arglurgl/rocketlogger/platformio/src/format_flash/format_flash.cpp

// modified Adafruit example to be called from main.cpp

// Adafruit SPI Flash FatFs Format Example
// Author: Tony DiCola
//
// !!!!!!!!!!!!!!!!!!!!!!!!!!!!!!!!!!!!!!!!!!!!!!!!!!!!!!!!!!!!!
// !!  NOTE: YOU WILL ERASE ALL DATA BY RUNNING THIS SKETCH!  !!
// !!!!!!!!!!!!!!!!!!!!!!!!!!!!!!!!!!!!!!!!!!!!!!!!!!!!!!!!!!!!!
//
// Usage:
// - Modify the pins and type of fatfs object in the config
//   section below if necessary (usually not necessary).
// - Upload this sketch to your M0 express board.
// - Open the serial monitor at 115200 baud.  You should see a
//   prompt to confirm formatting.  If you don't see the prompt
//   close the serial monitor, press the board reset buttton,
//   wait a few seconds, then open the serial monitor again.
// - Type OK and enter to confirm the format when prompted.
// - Partitioning and formatting will take about 30-60 seconds.
//   Once formatted a message will be printed to notify you that
//   it is finished.
//
#include <SPI.h>
#include <SdFat.h>
#include <Adafruit_SPIFlash.h>

// Since SdFat doesn't fully support FAT12 such as format a new flash
// We will use Elm Cham's fatfs f_mkfs() to format
#include "ff.h"
#include "diskio.h"

// up to 11 characters
#define DISK_LABEL    "EXT FLASH"

// for flashTransport definition
//#include "flash_config.h" already done in main

extern Adafruit_SPIFlash flash; //declared in main

void format_fat12(void)
{
  // Working buffer for f_mkfs.
  #ifdef __AVR__
    uint8_t workbuf[512];
  #else
    uint8_t workbuf[4096];
  #endif

  // Elm Cham's fatfs objects
  FATFS elmchamFatfs;

  // Make filesystem.
  FRESULT r = f_mkfs("", FM_FAT, 0, workbuf, sizeof(workbuf));
  if (r != FR_OK) {
    Serial.print(F("Error, f_mkfs failed with error code: ")); Serial.println(r, DEC);
    while(1) yield();
  }

  // mount to set disk label
  r = f_mount(&elmchamFatfs, "0:", 1);
  if (r != FR_OK) {
    Serial.print(F("Error, f_mount failed with error code: ")); Serial.println(r, DEC);
    while(1) yield();
  }

  // Setting label
  Serial.println(F("Setting disk label to: " DISK_LABEL));
  r = f_setlabel(DISK_LABEL);
  if (r != FR_OK) {
    Serial.print(F("Error, f_setlabel failed with error code: ")); Serial.println(r, DEC);
    while(1) yield();
  }

  // unmount
  f_unmount("0:");

  // sync to make sure all data is written to flash
  flash.syncBlocks();

  Serial.println(F("Formatted flash!"));
}

void check_fat12(void)
{
  // Check new filesystem
  FatVolume fatfs;
  if (!fatfs.begin(&flash)) {
    Serial.println(F("Error, failed to mount newly formatted filesystem!"));
    while(1) delay(1);
  }
}


void format_flash() {
  // serial port: wait for it to open before continuing.
  while (!Serial) delay(100);
  
  Serial.println(F("Adafruit SPI Flash FatFs Format Example"));

  // Initialize flash library and check its chip ID.
  if (!flash.begin()) {
    Serial.println(F("Error, failed to initialize flash chip!"));
    while(1) yield();
  }

  Serial.print(F("Flash chip JEDEC ID: 0x")); Serial.println(flash.getJEDECID(), HEX);
  Serial.print(F("Flash size: ")); Serial.print(flash.size() / 1024); Serial.println(F(" KB"));

  // Uncomment to flash LED while writing to flash
  // flash.setIndicator(LED_BUILTIN, true);

  // Wait for user to send OK to continue.
  Serial.setTimeout(30000);  // Increase timeout to print message less frequently.
  do {
    Serial.println(F("!!!!!!!!!!!!!!!!!!!!!!!!!!!!!!!!!!!!!!!!!!!!!!!!!!!!!!!!!!!!!!!!!!!!!"));
    Serial.println(F("This will ERASE ALL DATA on the flash chip and format it with a new filesystem!"));
    Serial.println(F("Type OK (all caps) and press enter to continue."));
    Serial.println(F("!!!!!!!!!!!!!!!!!!!!!!!!!!!!!!!!!!!!!!!!!!!!!!!!!!!!!!!!!!!!!!!!!!!!!"));
  } while ( !Serial.find((char*) "OK"));

  // Call fatfs begin and passed flash object to initialize file system
  Serial.println(F("Creating and formatting FAT filesystem (this takes ~60 seconds)..."));

  format_fat12();

  check_fat12();

  // Done!
  Serial.println(F("Flash chip successfully formatted with new empty filesystem! Please restart board."));

  while(1)
    {
      yield();
      delay(1);
    }
}

//--------------------------------------------------------------------+
// fatfs diskio
//--------------------------------------------------------------------+
extern "C"
{

DSTATUS disk_status ( BYTE pdrv )
{
  (void) pdrv;
	return 0;
}

DSTATUS disk_initialize ( BYTE pdrv )
{
  (void) pdrv;
	return 0;
}

DRESULT disk_read (
	BYTE pdrv,		/* Physical drive nmuber to identify the drive */
	BYTE *buff,		/* Data buffer to store read data */
	DWORD sector,	/* Start sector in LBA */
	UINT count		/* Number of sectors to read */
)
{
  (void) pdrv;
	return flash.readBlocks(sector, buff, count) ? RES_OK : RES_ERROR;
}

DRESULT disk_write (
	BYTE pdrv,			/* Physical drive nmuber to identify the drive */
	const BYTE *buff,	/* Data to be written */
	DWORD sector,		/* Start sector in LBA */
	UINT count			/* Number of sectors to write */
)
{
  (void) pdrv;
  return flash.writeBlocks(sector, buff, count) ? RES_OK : RES_ERROR;
}

DRESULT disk_ioctl (
	BYTE pdrv,		/* Physical drive nmuber (0..) */
	BYTE cmd,		/* Control code */
	void *buff		/* Buffer to send/receive control data */
)
{
  (void) pdrv;

  switch ( cmd )
  {
    case CTRL_SYNC:
      flash.syncBlocks();
      return RES_OK;

    case GET_SECTOR_COUNT:
      *((DWORD*) buff) = flash.size()/512;
      return RES_OK;

    case GET_SECTOR_SIZE:
      *((WORD*) buff) = 512;
      return RES_OK;

    case GET_BLOCK_SIZE:
      *((DWORD*) buff) = 8;    // erase block size in units of sector size
      return RES_OK;

    default:
      return RES_PARERR;
  }
}

}
